Aff314/AFF314MODKEEB/pics/wiring_guide.jpeg

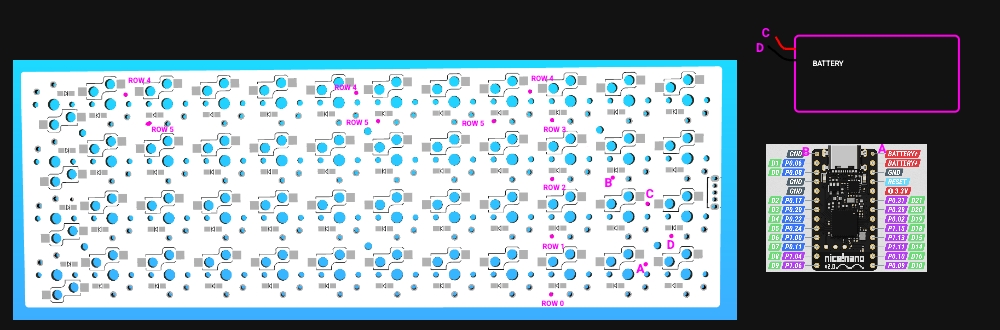
pics/wiring_guide.jpeg
